Soham-Nivargi/EEG-Acquisition-System/Handwritten Documentation/IMG-20240304-WA0019.jpg

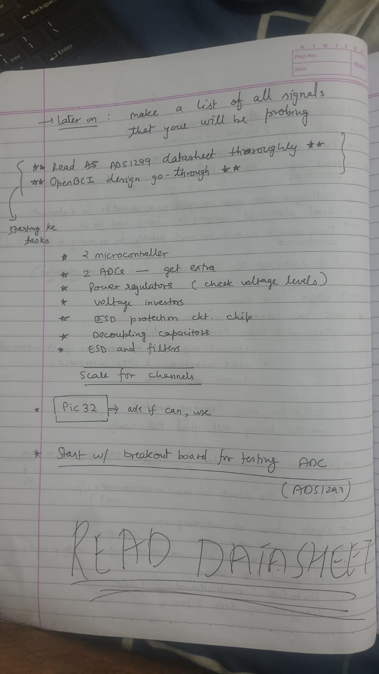
Handwritten Documentation/IMG-20240304-WA0019.jpg
